ollieelliot/STM32G0-WalkRunNN/Documentation_Photos_etc/Pin_Flash_Setup.PNG

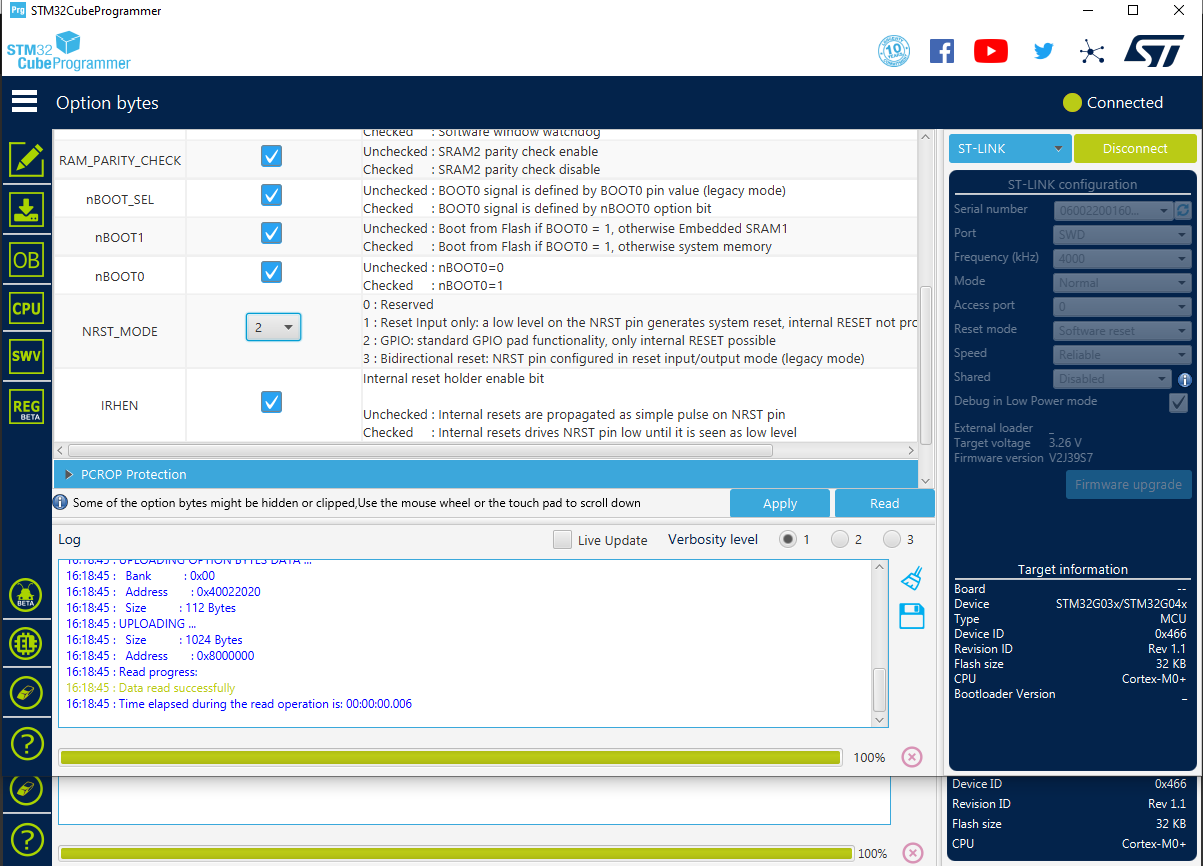
Documentation_Photos_etc/Pin_Flash_Setup.PNG
